benejoseph/coilbox/sinusoid_samples.h

#ifndef _SINUSOID_SAMPLES_H_
#define _SINUSOID_SAMPLES_H_
const static int16_t kSamples[16000] = {0,96,193,289,386,482,578,675,771,868,964,1060,1157,1253,1349,1445,1541,1637,1733,1829,1925,2021,2117,2212,2308,2404,2499,2594,2690,2785,2880,2975,3070,3164,3259,3353,3448,3542,3636,3730,3824,3918,4012,4105,4199,4292,4385,4478,4570,4663,4756,4848,4940,5032,5124,5215,5307,5398,5489,5580,5670,5761,5851,5941,6031,6120,6210,6299,6388,6477,6565,6654,6742,6830,6917,7005,7092,7179,7265,7352,7438,7524,7609,7694,7780,7864,7949,8033,8117,8201,8284,8367,8450,8533,8615,8697,8778,8860,8941,9022,9102,9182,9262,9341,9420,9499,9578,9656,9734,9811,9888,9965,10041,10117,10193,10268,10343,10418,10492,10566,10640,10713,10786,10858,10931,11002,11074,11144,11215,11285,11355,11424,11493,11562,11630,11698,11765,11832,11899,11965,12030,12096,12161,12225,12289,12353,12416,12479,12541,12603,12664,12725,12786,12846,12906,12965,13024,13082,13140,13197,13254,13311,13367,13422,13477,13532,13586,13640,13693,13746,13798,13850,13901,13952,14002,14052,14102,14150,14199,14247,14294,14341,14387,14433,14479,14524,14568,14612,14655,14698,14741,14782,14824,14865,14905,14945,14984,15023,15061,15099,15136,15173,15209,15244,15279,15314,15348,15381,15414,15447,15479,15510,15541,15571,15601,15630,15659,15687,15714,15741,15768,15794,15819,15844,15868,15892,15915,15938,15960,15981,16002,16023,16042,16062,16080,16099,16116,16133,16150,16166,16181,16196,16210,16224,16237,16249,16261,16273,16284,16294,16304,16313,16322,16330,16337,16344,16350,16356,16361,16366,16370,16373,16376,16379,16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
65,-9888,-9811,-9734,-9656,-9578,-9499,-9420,-9341,-9262,-9182,-9102,-9022,-8941,-8860,-8778,-8697,-8615,-8533,-8450,-8367,-8284,-8201,-8117,-8033,-7949,-7864,-7780,-7694,-7609,-7524,-7438,-7352,-7265,-7179,-7092,-7005,-6917,-6830,-6742,-6654,-6565,-6477,-6388,-6299,-6210,-6120,-6031,-5941,-5851,-5761,-5670,-5580,-5489,-5398,-5307,-5215,-5124,-5032,-4940,-4848,-4756,-4663,-4570,-4478,-4385,-4292,-4199,-4105,-4012,-3918,-3824,-3730,-3636,-3542,-3448,-3353,-3259,-3164,-3070,-2975,-2880,-2785,-2690,-2594,-2499,-2404,-2308,-2212,-2117,-2021,-1925,-1829,-1733,-1637,-1541,-1445,-1349,-1253,-1157,-1060,-964,-868,-771,-675,-578,-482,-386,-289,-193,-96,0};
const static uint32_t kNumSamples = 16000;
const static uint32_t kSampleRateHz = 16000;
#endif //_SINUSOID_SAMPLES_H_
